costamesatechsolutions/rackticker/docs/frames.png

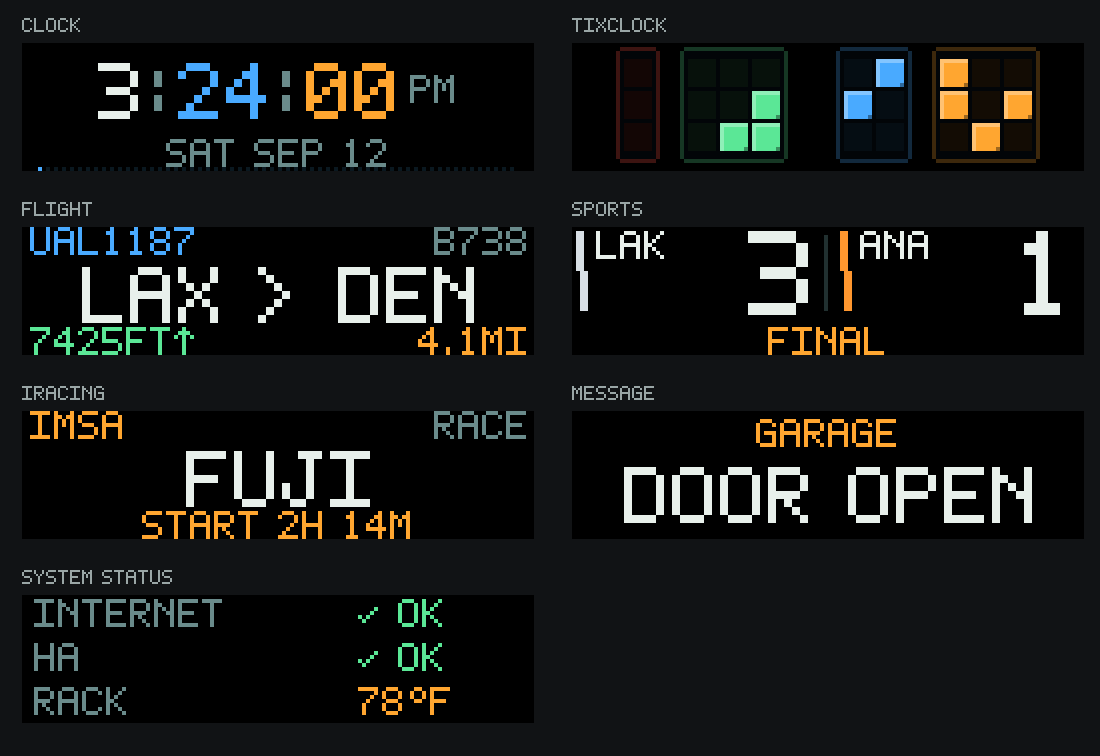
docs/frames.png
